szykes/nixie-tube-clock/test/led_mock.c

#include "led.h"

#include "mock.h"

void led_timer_interrupt(void) {
  mock_record(NULL, 0, NULL);
}

void led_is_dark_period(bool is_dark) {
  type_st params[] = {
    {
      .type = TYPE_BOOL,
      .value = &is_dark,
      .size = sizeof(is_dark),
    }
  };
  mock_record(params, sizeof(params)/sizeof(type_st), NULL);
}
